Picatout/metal-pointer/KiCAD/bare-metal.kicad_sch

## KiCad design KiCAD/bare-metal.kicad_sch (2023-03-25)

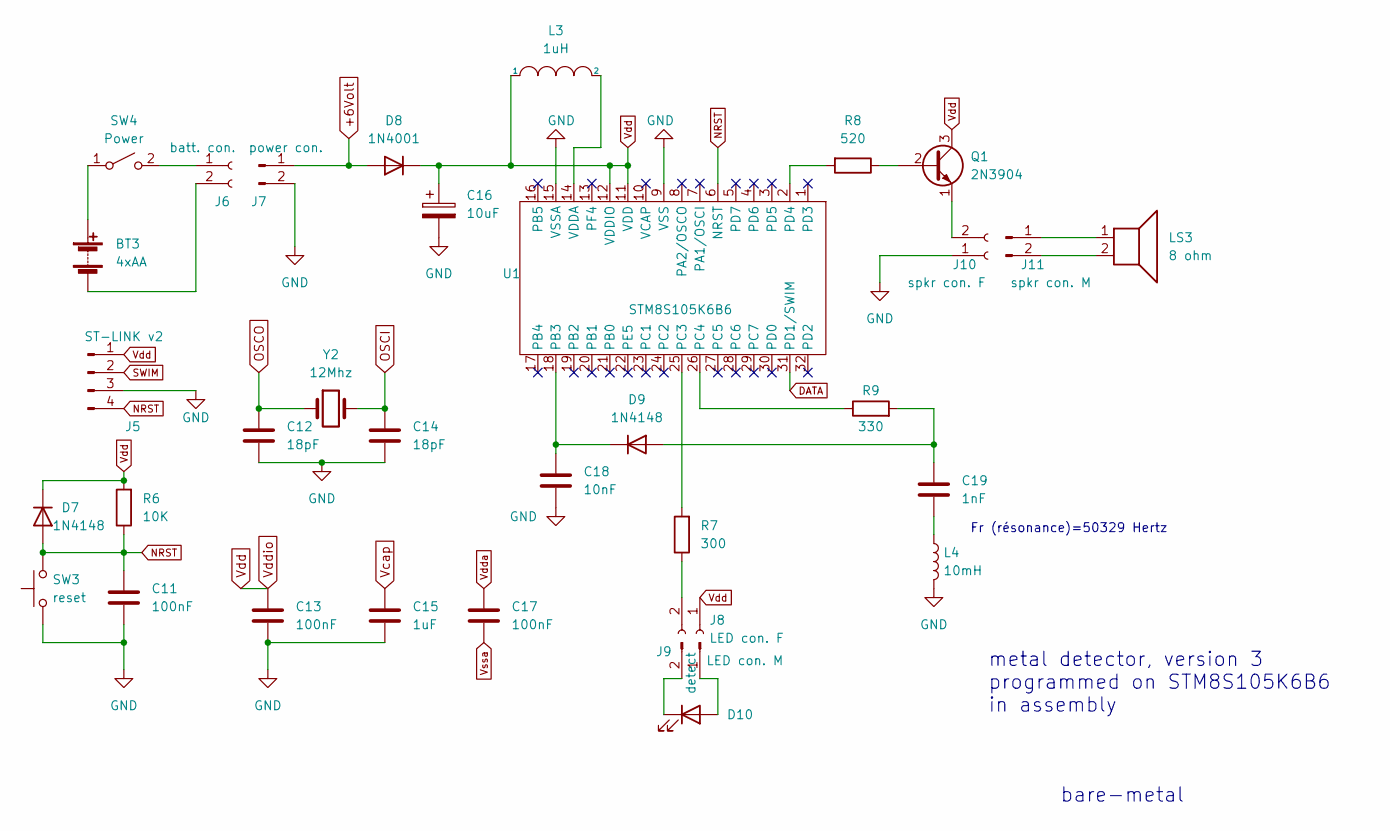
[picture p18: schematic bare-metal.kicad_sch]

Parts:
BT3: 4xAA
C11, C13, C17: 100nF
C12, C14: 18pF
C15: 1uF
C16: 10uF
C18: 10nF
C19: 1nF
D7: 1N4148; D_DO-41_SOD81_P10.16mm_Horizontal
D8: 1N4001; D_DO-41_SOD81_P10.16mm_Horizontal
D9: 1N4148; D_DO-35_SOD27_P7.62mm_Horizontal
D10: detect
J5: ST-LINK v2
J6: batt. con.
J7: power con.
J8: LED con. F
J9: LED con. M
J10: spkr con. F
J11: spkr con. M
L3: 1uH
L4: 10mH
LS3: 8 ohm
Q1: 2N3904; TO-92_Inline
R6: 10K
R7: 300
R8: 520
R9: 330
SW3: reset
SW4: Power
U1: STM8S105K6B6
Y2: 12Mhz

Connections:
+6Volt: D8.2 (A), J7.1
DATA: U1.31 (PD1/SWIM)
GND: C11.2, C12.2, C13.2, C14.2, C15.2, C16.2, C18.1, J5.3, J7.2, J10.1, L4.2, SW3.1 (A), SW3.2 (A), U1.9 (VSS), U1.15 (VSSA)
NRST: C11.1, D7.2 (A), J5.4, R6.1, SW3.3 (B), SW3.4 (B), U1.6 (NRST)
unnamed: BT3.1 (+), SW4.1 (A)
unnamed: BT3.2 (-), J6.2
unnamed: C18.2, D9.1 (K), U1.18 (PB3)
unnamed: C19.1, D9.2 (A), R9.2
unnamed: C19.2, L4.1
unnamed: D10.1 (K), J9.2
unnamed: D10.2 (A), J9.1
unnamed: J6.1, SW4.2 (B)
unnamed: J8.2, R7.1
unnamed: J10.2, Q1.1 (E)
unnamed: J11.1, LS3.1
unnamed: J11.2, LS3.2
unnamed: L3.2, U1.14 (VDDA)
unnamed: Q1.2 (B), R8.1
unnamed: R7.2, U1.25 (PC3)
unnamed: R8.2, U1.2 (PD4)
unnamed: R9.1, U1.26 (PC4)
OSCI: C14.1, Y2.2
OSCO: C12.1, Y2.1
SWIM: J5.2
Vcap: C15.1
Vdd: C13.1, C16.1, D7.1 (K), D8.1 (K), J5.1, J8.1, L3.1, Q1.3 (C), R6.2, U1.11 (VDD), U1.12 (VDDIO)
Vdda: C17.1
Vssa: C17.2

Notes on the sheet:
Fr (résonance)=50329 Hertz
bare-metal
metal detector, version 3 programmed on STM8S105K6B6 in assembly
