Picatout/metal-pointer/KiCAD/nail-detector.v5.kicad_sch

## KiCad design KiCAD/nail-detector.v5.kicad_sch (2023-03-24)

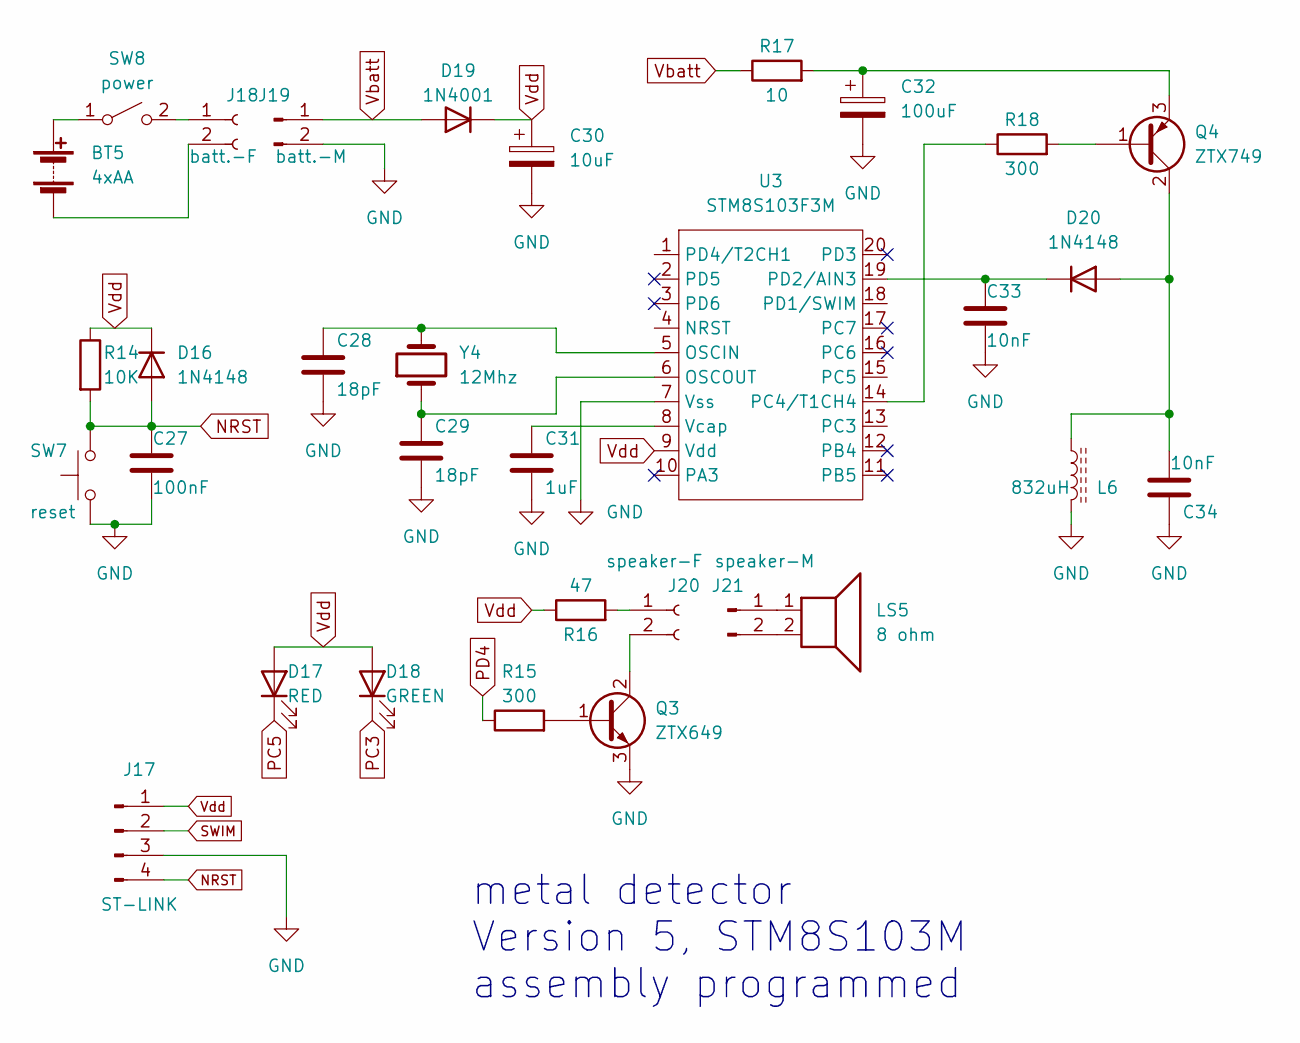
[picture p19: schematic nail-detector.v5.kicad_sch]

Parts:
BT5: 4xAA
C27: 100nF
C28, C29: 18pF
C30: 10uF
C31: 1uF
C32: 100uF
C33, C34: 10nF
D16, D20: 1N4148; D_DO-35_SOD27_P7.62mm_Horizontal
D17: RED
D18: GREEN
D19: 1N4001; D_DO-41_SOD81_P10.16mm_Horizontal
J17: ST-LINK
J18: batt.-F
J19: batt.-M
J20: speaker-F
J21: speaker-M
L6: 832uH
LS5: 8 ohm
Q3: ZTX649
Q4: ZTX749
R14: 10K
R15, R18: 300
R16: 47
R17: 10
SW7: reset
SW8: power
U3: STM8S103F3M
Y4: 12Mhz

Connections:
GND: C27.2, C28.2, C29.2, C30.2, C31.2, C32.2, C33.2, C34.2, J17.3, J19.2, L6.2, Q3.3 (E), SW7.1 (A), SW7.2 (A), U3.7 (Vss)
NRST: C27.1, D16.2 (A), J17.4, R14.2, SW7.3 (B), SW7.4 (B)
unnamed: BT5.1 (+), SW8.1 (A)
unnamed: BT5.2 (-), J18.2
unnamed: C28.1, U3.5 (OSCIN), Y4.2
unnamed: C29.1, U3.6 (OSCOUT), Y4.1
unnamed: C31.1, U3.8 (Vcap)
unnamed: C32.1, Q4.3 (E), R17.2
unnamed: C33.1, D20.1 (K), U3.19 (PD2/AIN3)
unnamed: C34.1, D20.2 (A), L6.1, Q4.2 (C)
unnamed: J18.1, SW8.2 (B)
unnamed: J20.1, R16.2
unnamed: J20.2, Q3.2 (C)
unnamed: J21.1, LS5.1
unnamed: J21.2, LS5.2
unnamed: Q3.1 (B), R15.2
unnamed: Q4.1 (B), R18.2
unnamed: R18.1, U3.14 (PC4/T1CH4)
PC3: D18.1 (K)
PC5: D17.1 (K)
PD4: R15.1
SWIM: J17.2
Vbatt: D19.2 (A), J19.1, R17.1
Vdd: C30.1, D16.1 (K), D17.2 (A), D18.2 (A), D19.1 (K), J17.1, R14.1, R16.1, U3.9 (Vdd)

Notes on the sheet:
metal detector Version 5, STM8S103M assembly programmed
