Picatout/metal-pointer/KiCAD/pin-point-metal-detector.kicad_sch

## KiCad design KiCAD/pin-point-metal-detector.kicad_sch (2023-03-25)

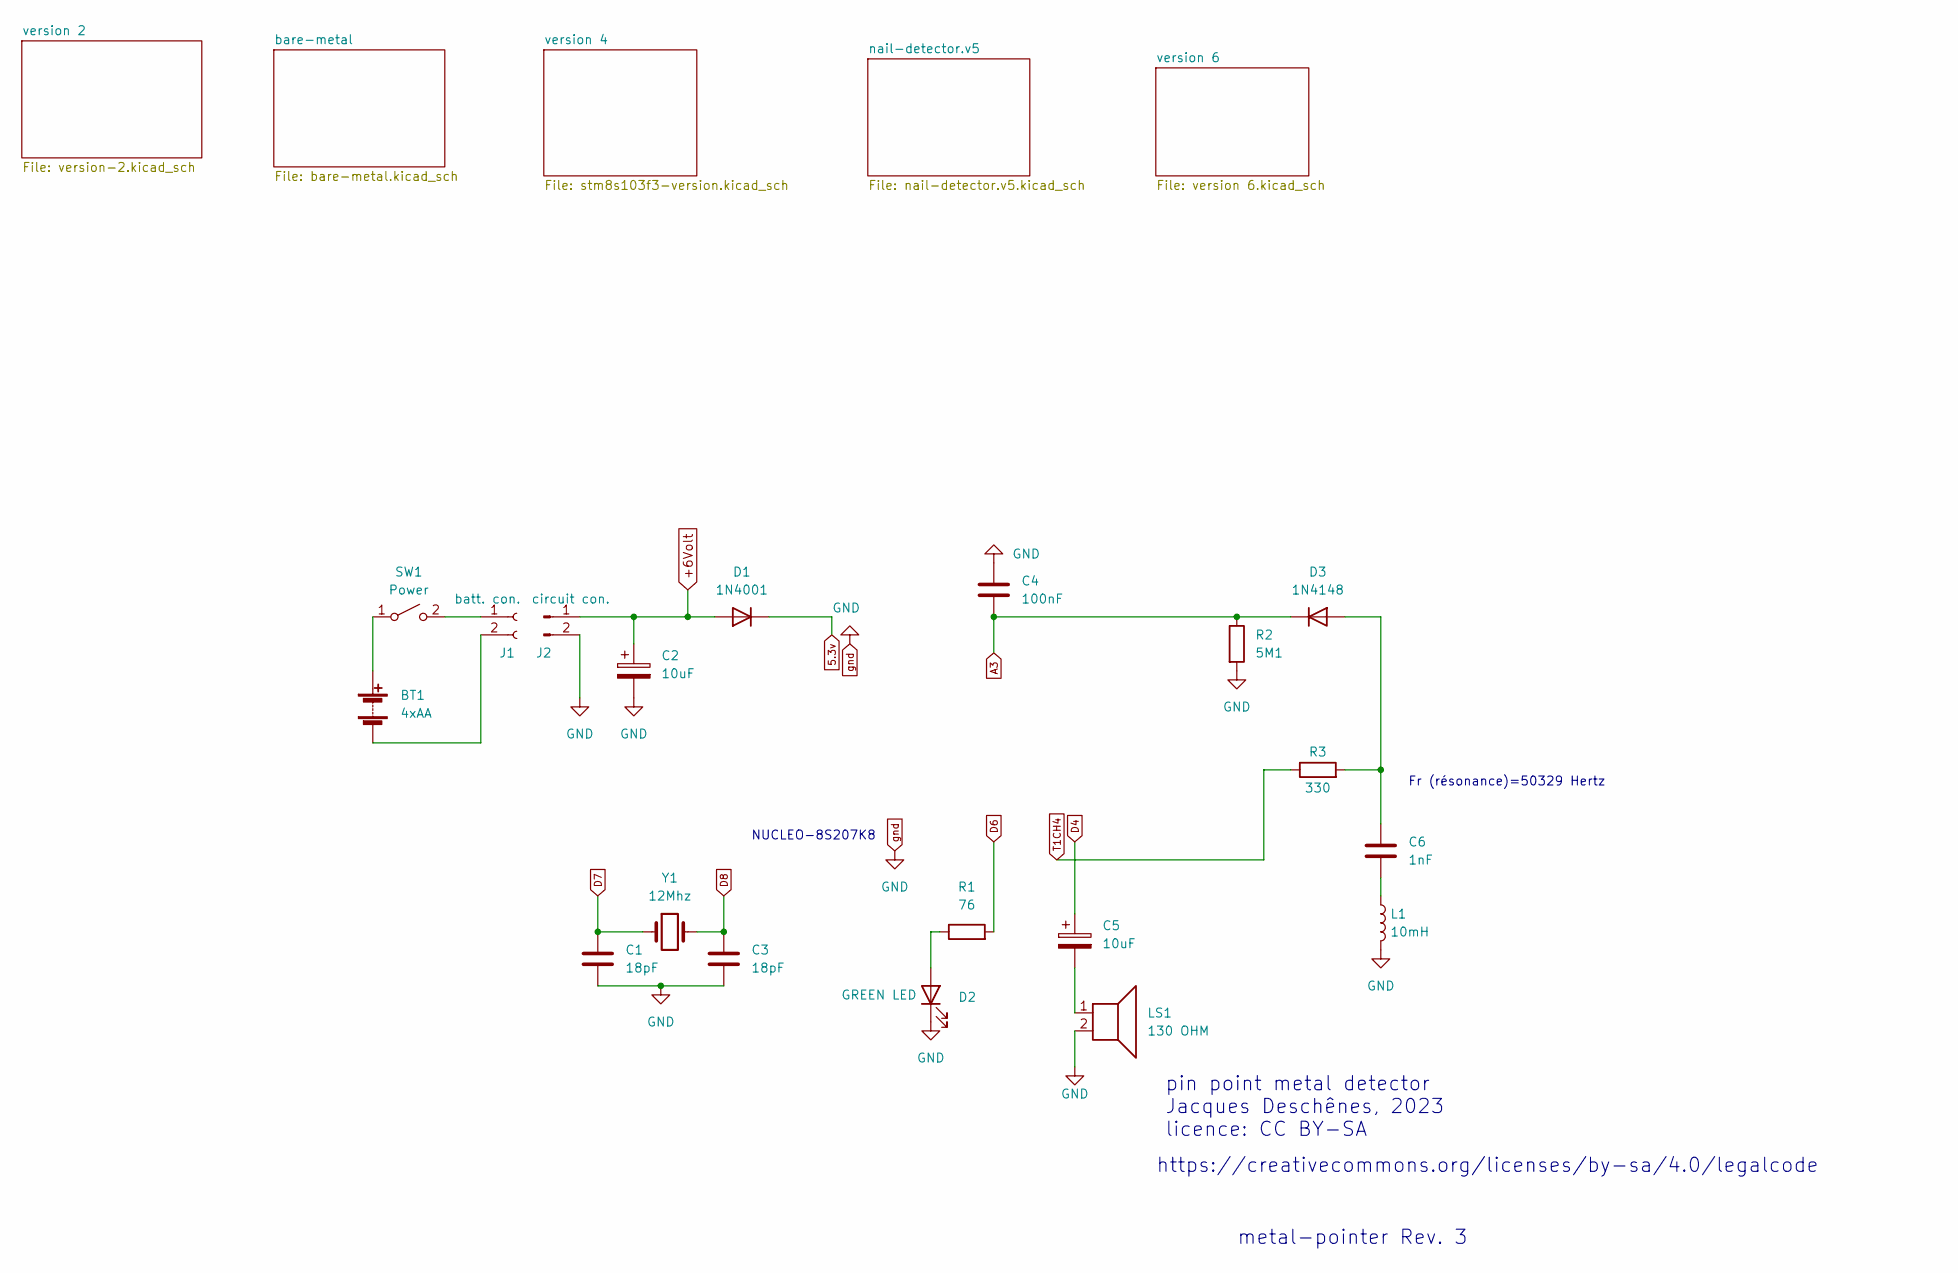
[picture p20: schematic pin-point-metal-detector.kicad_sch]

Parts:
BT1: 4xAA
C1, C3: 18pF
C2, C5: 10uF
C4: 100nF
C6: 1nF
D1: 1N4001; D_DO-41_SOD81_P10.16mm_Horizontal
D2: GREEN LED
D3: 1N4148; D_DO-35_SOD27_P7.62mm_Horizontal
J1: batt. con.
J2: circuit con.
L1: 10mH
LS1: 130 OHM
R1: 76
R2: 5M1
R3: 330
SW1: Power
Y1: 12Mhz

Connections:
5.3v: D1.1 (K)
+6Volt: C2.1, D1.2 (A), J2.1
A3: C4.2, D3.1 (K), R2.1
D4: C5.1
D6: R1.2
D7: C1.1, Y1.1
D8: C3.1, Y1.2
unnamed: BT1.1 (+), SW1.1 (A)
unnamed: BT1.2 (-), J1.2
unnamed: C5.2, LS1.1
unnamed: C6.1, D3.2 (A), R3.2
unnamed: C6.2, L1.1
unnamed: D2.2 (A), R1.1
unnamed: J1.1, SW1.2 (B)
T1CH4: R3.1
gnd: C1.2, C2.2, C3.2, C4.1, D2.1 (K), J2.2, L1.2, LS1.2, R2.2

Notes on the sheet:
Fr (résonance)=50329 Hertz
https://creativecommons.org/licenses/by-sa/4.0/legalcode
NUCLEO-8S207K8
metal-pointer Rev. 3
pin point metal detector Jacques Deschênes, 2023 licence: CC BY-SA
