Picatout/metal-pointer/KiCAD/stm8s103f3-version.kicad_sch

## KiCad design KiCAD/stm8s103f3-version.kicad_sch (2023-03-24)

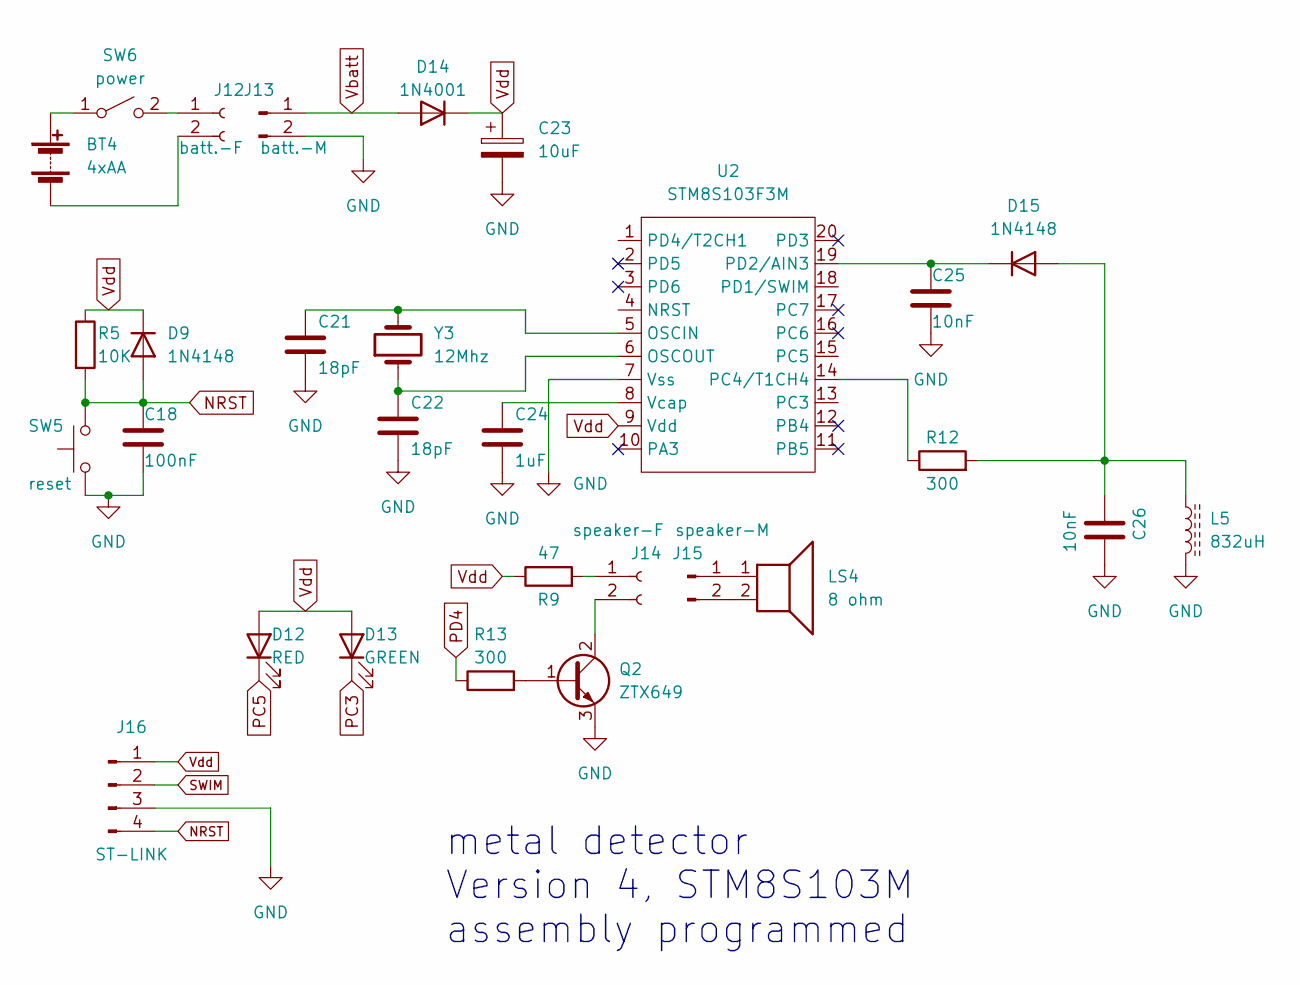
[picture p21: schematic stm8s103f3-version.kicad_sch]

Parts:
BT4: 4xAA
C18: 100nF
C21, C22: 18pF
C23: 10uF
C24: 1uF
C25, C26: 10nF
D9, D15: 1N4148; D_DO-35_SOD27_P7.62mm_Horizontal
D12: RED
D13: GREEN
D14: 1N4001; D_DO-41_SOD81_P10.16mm_Horizontal
J12: batt.-F
J13: batt.-M
J14: speaker-F
J15: speaker-M
J16: ST-LINK
L5: 832uH
LS4: 8 ohm
Q2: ZTX649
R5: 10K
R9: 47
R12, R13: 300
SW5: reset
SW6: power
U2: STM8S103F3M
Y3: 12Mhz

Connections:
GND: C18.2, C21.2, C22.2, C23.2, C24.2, C25.2, C26.2, J13.2, J16.3, L5.2, Q2.3 (E), SW5.1 (A), SW5.2 (A), U2.7 (Vss)
NRST: C18.1, D9.2 (A), J16.4, R5.2, SW5.3 (B), SW5.4 (B)
unnamed: BT4.1 (+), SW6.1 (A)
unnamed: BT4.2 (-), J12.2
unnamed: C21.1, U2.5 (OSCIN), Y3.2
unnamed: C22.1, U2.6 (OSCOUT), Y3.1
unnamed: C24.1, U2.8 (Vcap)
unnamed: C25.1, D15.1 (K), U2.19 (PD2/AIN3)
unnamed: C26.1, D15.2 (A), L5.1, R12.2
unnamed: J12.1, SW6.2 (B)
unnamed: J14.1, R9.2
unnamed: J14.2, Q2.2 (C)
unnamed: J15.1, LS4.1
unnamed: J15.2, LS4.2
unnamed: Q2.1 (B), R13.2
unnamed: R12.1, U2.14 (PC4/T1CH4)
PC3: D13.1 (K)
PC5: D12.1 (K)
PD4: R13.1
SWIM: J16.2
Vbatt: D14.2 (A), J13.1
Vdd: C23.1, D9.1 (K), D12.2 (A), D13.2 (A), D14.1 (K), J16.1, R5.1, R9.1, U2.9 (Vdd)

Notes on the sheet:
metal detector Version 4, STM8S103M assembly programmed
