Picatout/metal-pointer/KiCAD/version 6.kicad_sch

## KiCad design KiCAD/version 6.kicad_sch (2023-03-25)

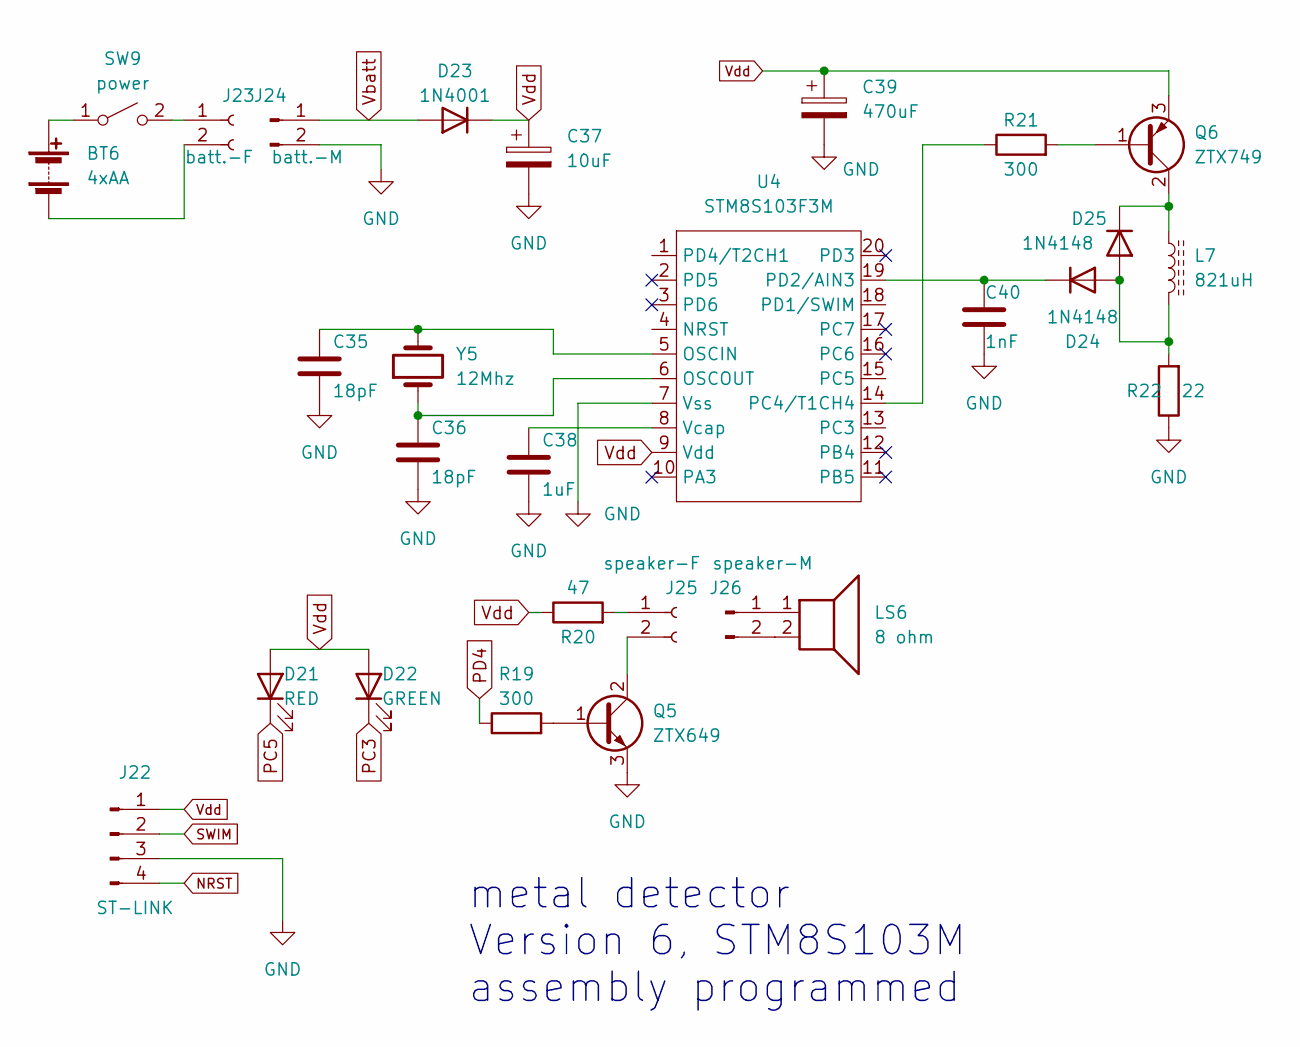
[picture p22: schematic version 6.kicad_sch]

Parts:
BT6: 4xAA
C35, C36: 18pF
C37: 10uF
C38: 1uF
C39: 470uF
C40: 1nF
D21: RED
D22: GREEN
D23: 1N4001; D_DO-41_SOD81_P10.16mm_Horizontal
D24, D25: 1N4148; D_DO-35_SOD27_P7.62mm_Horizontal
J22: ST-LINK
J23: batt.-F
J24: batt.-M
J25: speaker-F
J26: speaker-M
L7: 821uH
LS6: 8 ohm
Q5: ZTX649
Q6: ZTX749
R19, R21: 300
R20: 47
R22: 22
SW9: power
U4: STM8S103F3M
Y5: 12Mhz

Connections:
GND: C35.2, C36.2, C37.2, C38.2, C39.2, C40.2, J22.3, J24.2, Q5.3 (E), R22.1, U4.7 (Vss)
NRST: J22.4
unnamed: BT6.1 (+), SW9.1 (A)
unnamed: BT6.2 (-), J23.2
unnamed: C35.1, U4.5 (OSCIN), Y5.2
unnamed: C36.1, U4.6 (OSCOUT), Y5.1
unnamed: C38.1, U4.8 (Vcap)
unnamed: C40.1, D24.1 (K), U4.19 (PD2/AIN3)
unnamed: D24.2 (A), D25.2 (A), L7.2, R22.2
unnamed: D25.1 (K), L7.1, Q6.2 (C)
unnamed: J23.1, SW9.2 (B)
unnamed: J25.1, R20.2
unnamed: J25.2, Q5.2 (C)
unnamed: J26.1, LS6.1
unnamed: J26.2, LS6.2
unnamed: Q5.1 (B), R19.2
unnamed: Q6.1 (B), R21.2
unnamed: R21.1, U4.14 (PC4/T1CH4)
PC3: D22.1 (K)
PC5: D21.1 (K)
PD4: R19.1
SWIM: J22.2
Vbatt: D23.2 (A), J24.1
Vdd: C37.1, C39.1, D21.2 (A), D22.2 (A), D23.1 (K), J22.1, Q6.3 (E), R20.1, U4.9 (Vdd)

Notes on the sheet:
metal detector Version 6, STM8S103M assembly programmed
