Picatout/metal-pointer/KiCAD/version-2.kicad_sch

## KiCad design KiCAD/version-2.kicad_sch (2023-03-25, an earlier design)

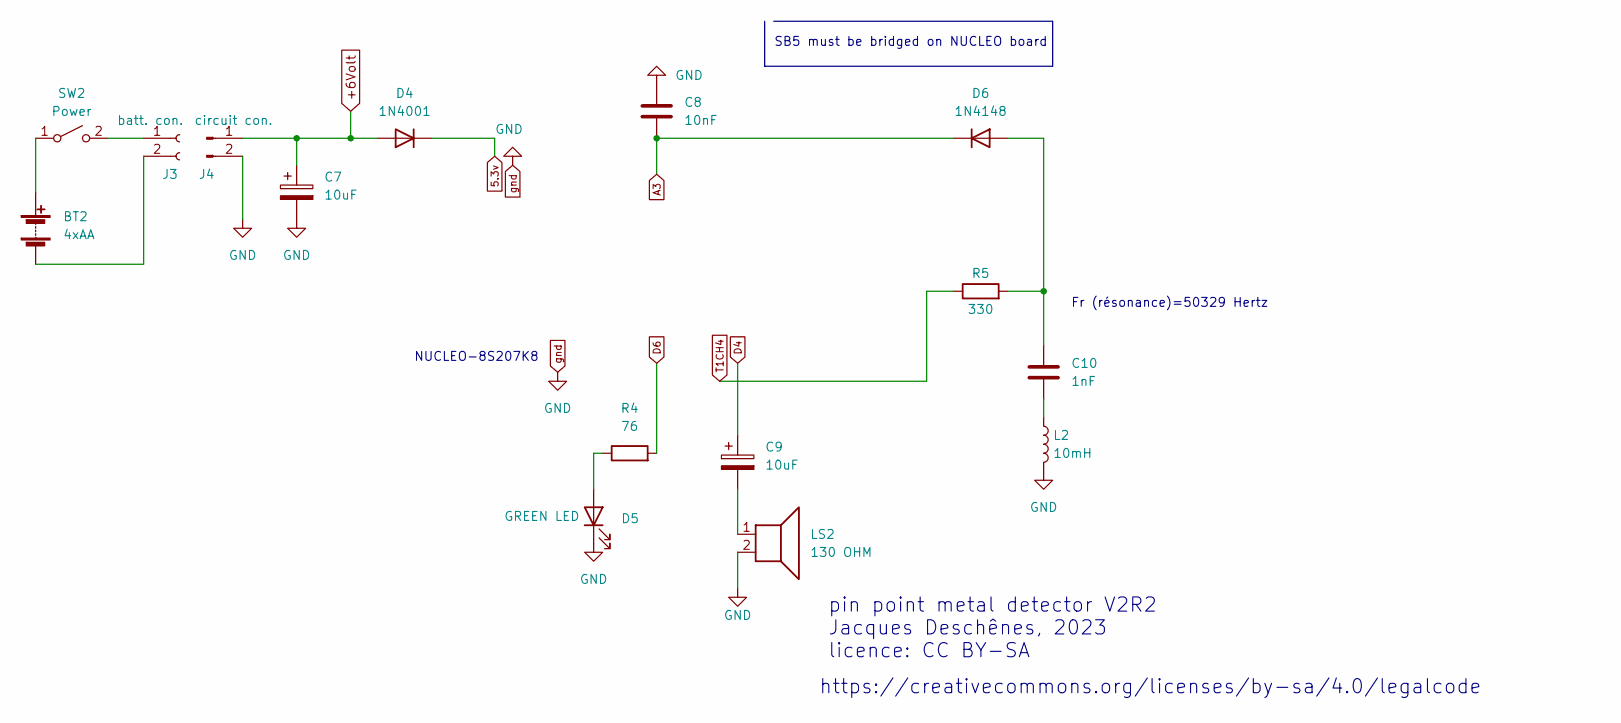
[picture p23: schematic version-2.kicad_sch]

Parts:
BT2: 4xAA
C7, C9: 10uF
C8: 10nF
C10: 1nF
D4: 1N4001; D_DO-41_SOD81_P10.16mm_Horizontal
D5: GREEN LED
D6: 1N4148; D_DO-35_SOD27_P7.62mm_Horizontal
J3: batt. con.
J4: circuit con.
L2: 10mH
LS2: 130 OHM
R4: 76
R5: 330
SW2: Power

Connections:
5.3v: D4.1 (K)
+6Volt: C7.1, D4.2 (A), J4.1
A3: C8.2, D6.1 (K)
D4: C9.1
D6: R4.2
unnamed: BT2.1 (+), SW2.1 (A)
unnamed: BT2.2 (-), J3.2
unnamed: C9.2, LS2.1
unnamed: C10.1, D6.2 (A), R5.2
unnamed: C10.2, L2.1
unnamed: D5.2 (A), R4.1
unnamed: J3.1, SW2.2 (B)
T1CH4: R5.1
gnd: C7.2, C8.1, D5.1 (K), J4.2, L2.2, LS2.2

Notes on the sheet:
pin point metal detector V2R2 Jacques Deschênes, 2023 licence: CC BY-SA
Fr (résonance)=50329 Hertz
SB5 must be bridged on NUCLEO board
NUCLEO-8S207K8
https://creativecommons.org/licenses/by-sa/4.0/legalcode
