Picatout/metal-pointer/KiCAD/nail-finder/nail-finder.kicad_sch

## KiCad design KiCAD/nail-finder/nail-finder.kicad_sch (2023-04-05, an earlier design)

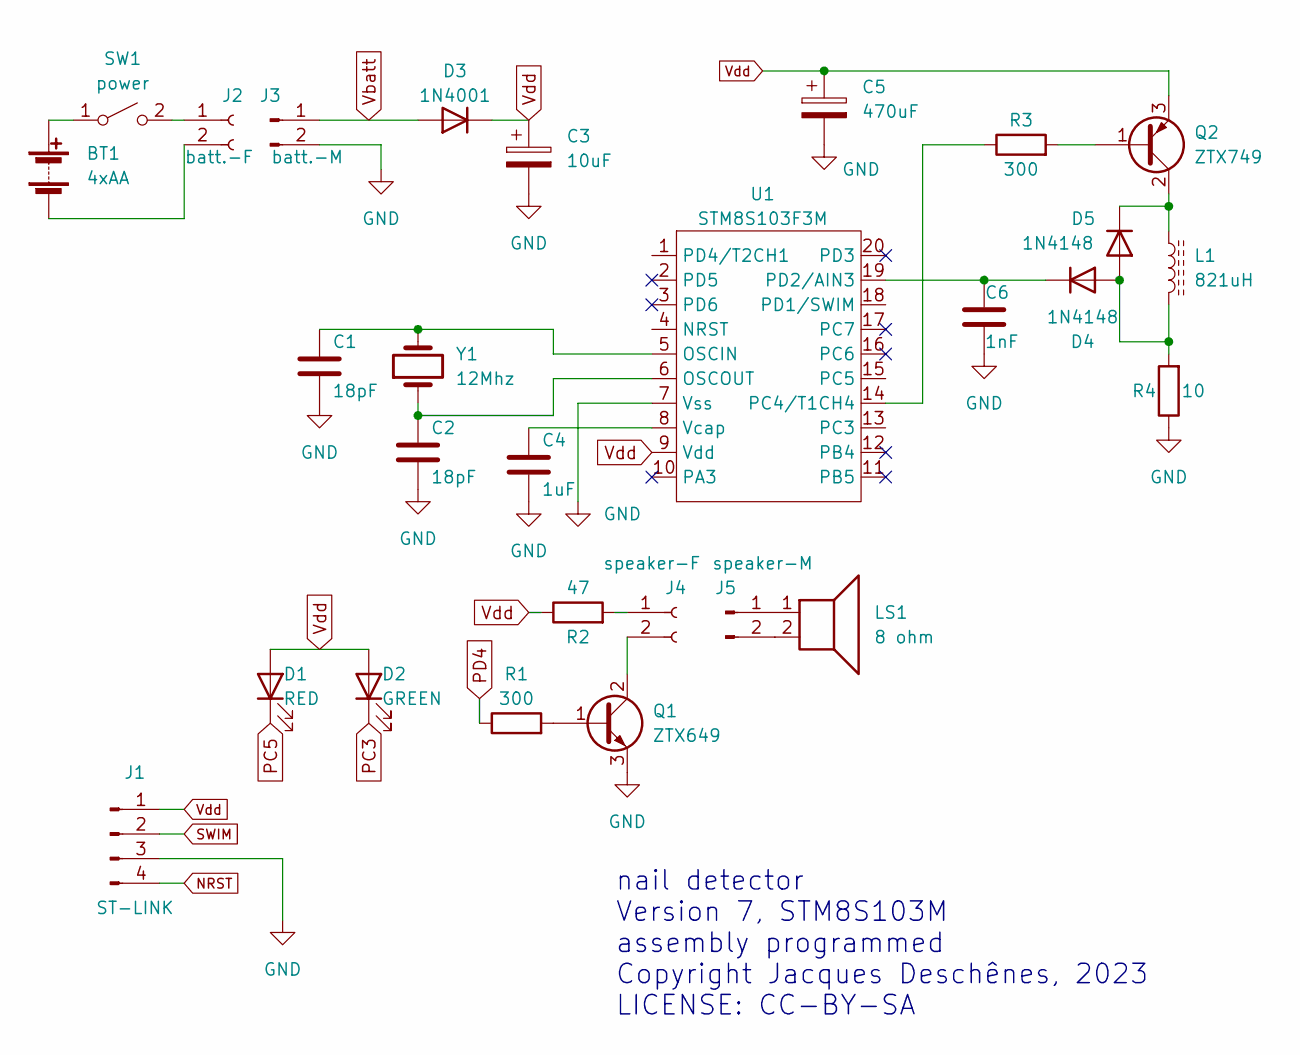
[picture p24: schematic nail-finder.kicad_sch]

Parts:
BT1: 4xAA
C1, C2: 18pF
C3: 10uF
C4: 1uF
C5: 470uF
C6: 1nF
D1: RED
D2: GREEN
D3: 1N4001; D_DO-41_SOD81_P10.16mm_Horizontal
D4, D5: 1N4148; D_DO-35_SOD27_P7.62mm_Horizontal
J1: ST-LINK
J2: batt.-F
J3: batt.-M
J4: speaker-F
J5: speaker-M
L1: 821uH
LS1: 8 ohm
Q1: ZTX649
Q2: ZTX749
R1, R3: 300
R2: 47
R4: 10
SW1: power
U1: STM8S103F3M
Y1: 12Mhz

Connections:
GND: C1.2, C2.2, C3.2, C4.2, C5.2, C6.2, J1.3, J3.2, Q1.3 (E), R4.1, U1.7 (Vss)
NRST: J1.4
unnamed: BT1.1 (+), SW1.1 (A)
unnamed: BT1.2 (-), J2.2
unnamed: C1.1, U1.5 (OSCIN), Y1.2
unnamed: C2.1, U1.6 (OSCOUT), Y1.1
unnamed: C4.1, U1.8 (Vcap)
unnamed: C6.1, D4.1 (K), U1.19 (PD2/AIN3)
unnamed: D4.2 (A), D5.2 (A), L1.2, R4.2
unnamed: D5.1 (K), L1.1, Q2.2 (C)
unnamed: J2.1, SW1.2 (B)
unnamed: J4.1, R2.2
unnamed: J4.2, Q1.2 (C)
unnamed: J5.1, LS1.1
unnamed: J5.2, LS1.2
unnamed: Q1.1 (B), R1.2
unnamed: Q2.1 (B), R3.2
unnamed: R3.1, U1.14 (PC4/T1CH4)
PC3: D2.1 (K)
PC5: D1.1 (K)
PD4: R1.1
SWIM: J1.2
Vbatt: D3.2 (A), J3.1
Vdd: C3.1, C5.1, D1.2 (A), D2.2 (A), D3.1 (K), J1.1, Q2.3 (E), R2.1, U1.9 (Vdd)

Notes on the sheet:
nail detector Version 7, STM8S103M assembly programmed Copyright Jacques Deschênes, 2023 LICENSE: CC-BY-SA
